jpt1729/lp-kbb/photos/Screenshot 2025-07-27 214902.png

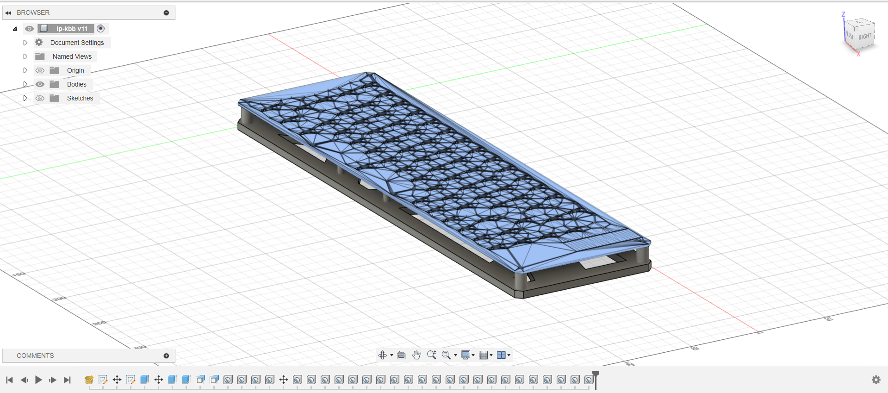
photos/Screenshot 2025-07-27 214902.png
