jpt1729/lp-kbb/photos/Screenshot 2025-07-27 215655.png

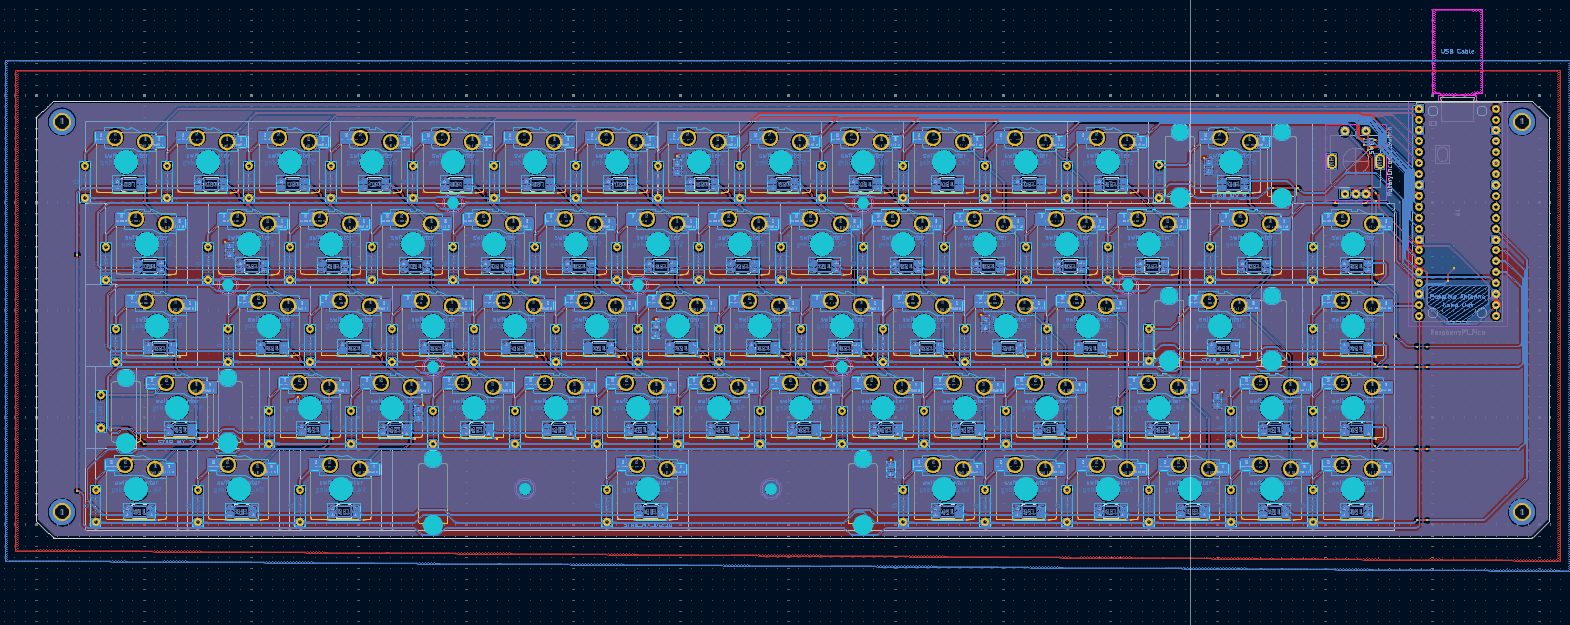
photos/Screenshot 2025-07-27 215655.png
