jpt1729/lp-kbb/photos/complete-assembly.png

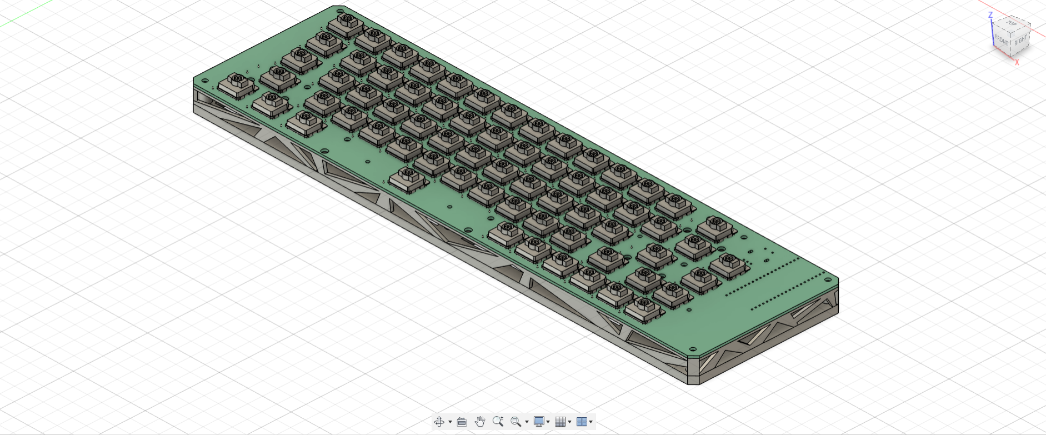
photos/complete-assembly.png
